CucumberWorks/CG_RigidCon/STLs/CG_RigidCon/MR.stl

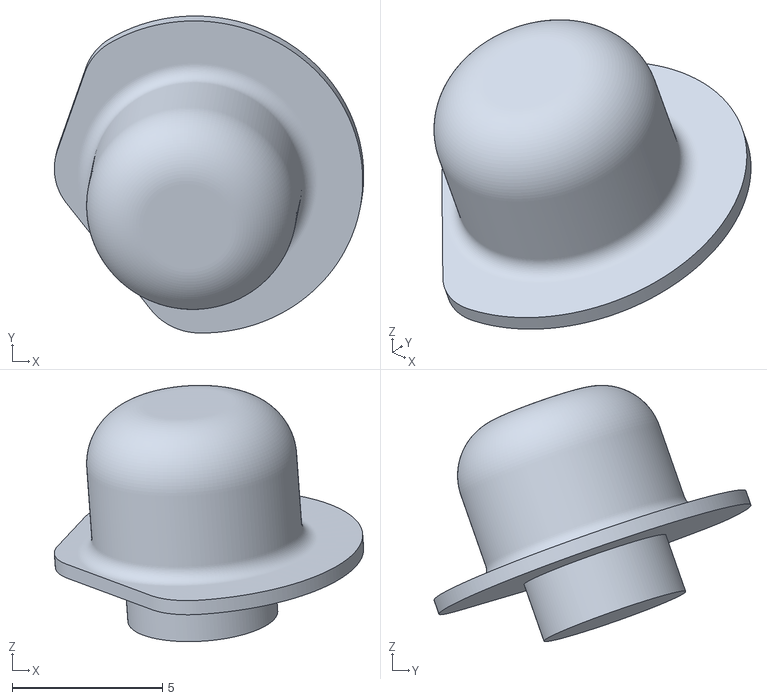
[picture p35: CAD file, 2023-12-10]
STLs/CG_RigidCon/MR.stl
10.3 x 10.5 x 8.53
