CucumberWorks/CG_RigidCon/img/instruction/base/IMG_7848.jpeg

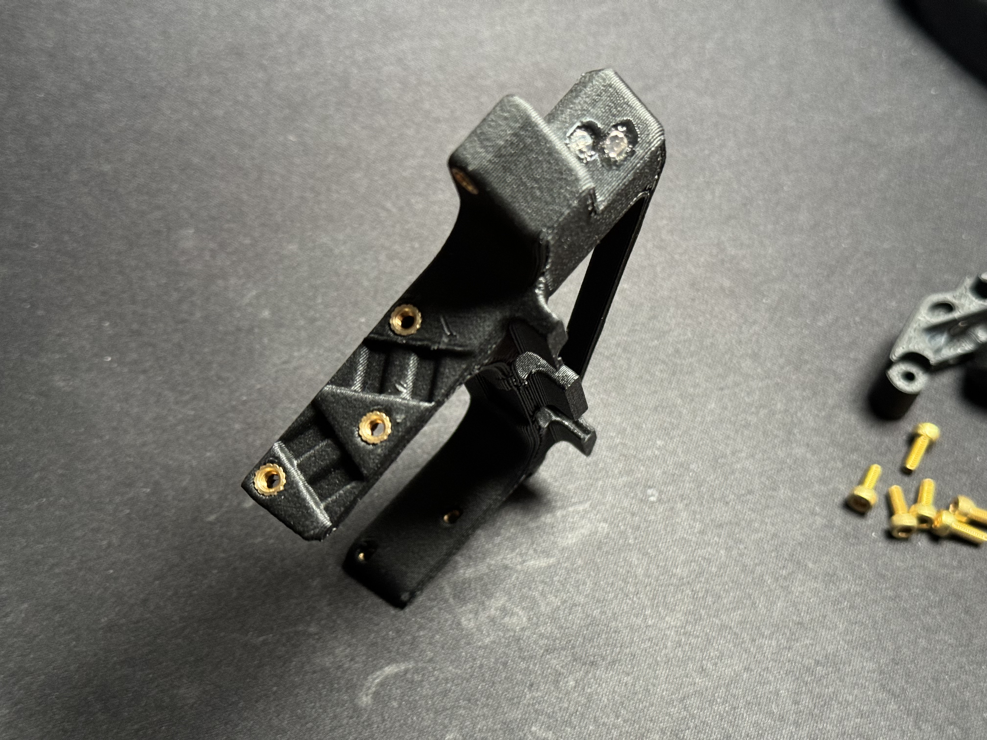
img/instruction/base/IMG_7848.jpeg
