CucumberWorks/CG_RigidCon/img/instruction/base/IMG_7853.jpeg

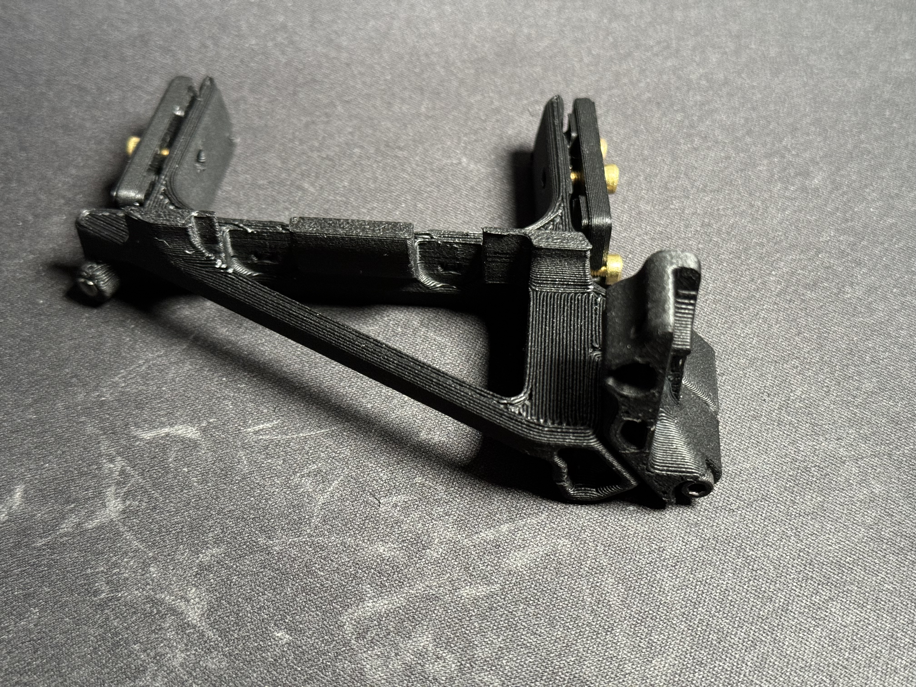
img/instruction/base/IMG_7853.jpeg
